pioupiou-archive/pioupiou-v0/pcb/pcb-pdf/pioupiou-v0.2-F_SilkS.pdf

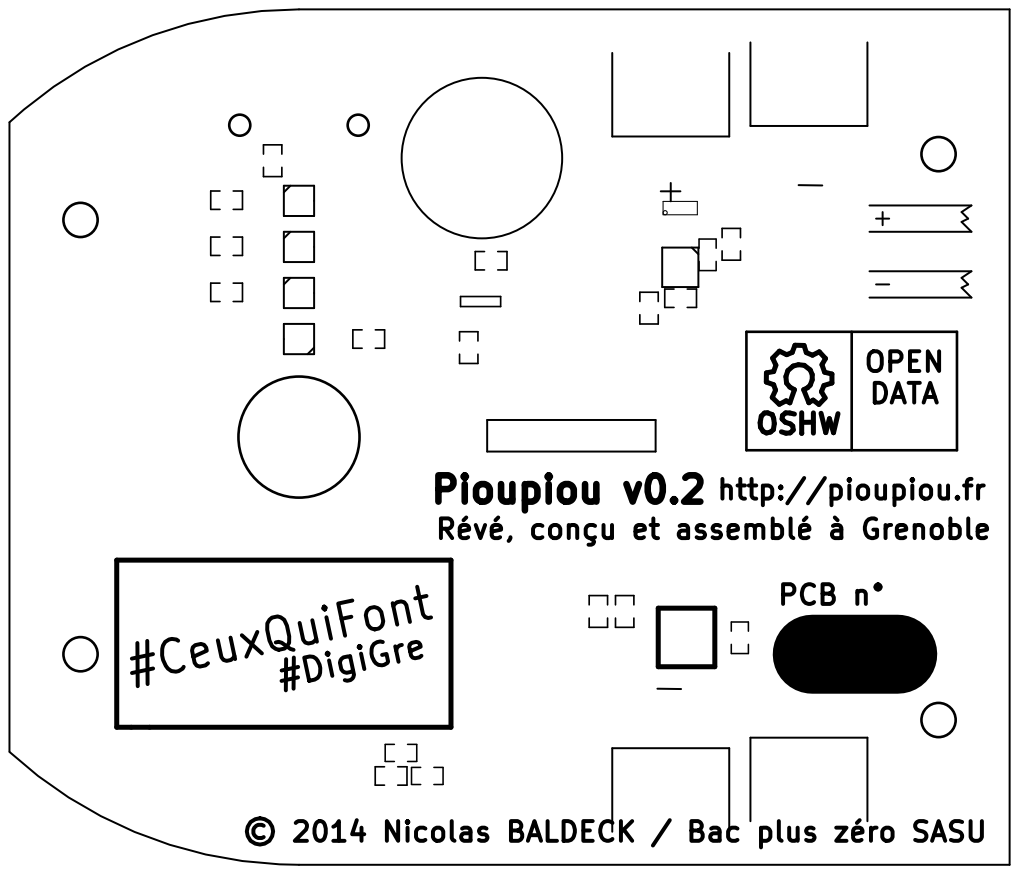
[picture p3: page 1]

Révé, conçu et assemblé à Grenoble

PCB n° © 2014 Nicolas BALDECK / Bac plus zéro SASU

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
